Farnaz03/RoboticStudyCompanion/CodeStation/TestCodes/aiy_button.py

from aiy.board import Board, Led

def main():
    print('LED is ON while button is pressed (Ctrl-C for exit).')
    with Board() as board:
        while True:
            board.button.wait_for_press()
            print('ON')
            board.led.state = Led.ON
            board.button.wait_for_release()
            print('OFF')
            board.led.state = Led.OFF


if __name__ == '__main__':
    main()
