Farnaz03/RoboticStudyCompanion/CodeStation/TestCodes/gpio_neopixel.py

# from time import sleep
# import neopixel
# from gpiozero import LED
# from aiy.pins import BUZZER_GPIO_PIN
# print(BUZZER_GPIO_PIN)
# # Define the number of pixels in the NeoPixel ring
# NUM_PIXELS = 16

# # Initialize the NeoPixel ring
# # led = LED(PIN_B)
# print(PIN_B)
# pixels = neopixel.NeoPixel(1, NUM_PIXELS)

# while True:
#         led.on()
#         sleep(1)
#         led.off()
#         sleep(1)

#####################################################

# import board
# import neopixel
# pixels = neopixel.NeoPixel(22, 16)
# pixels.fill((0, 100, 0))

# # Set the color of all pixels to green
# pixels.fill((0, 255, 0))
# pixels.show()

# # Wait for 2 seconds
# time.sleep(2)

# # Turn off all LEDs
# pixels.fill((0, 0, 0))
# pixels.show()
